dcooperdalrymple/kaypro-usb-keyboard-adapter/hardware/kaypro-usb.kicad_sch

## KiCad design hardware/kaypro-usb.kicad_sch (2023-10-24)

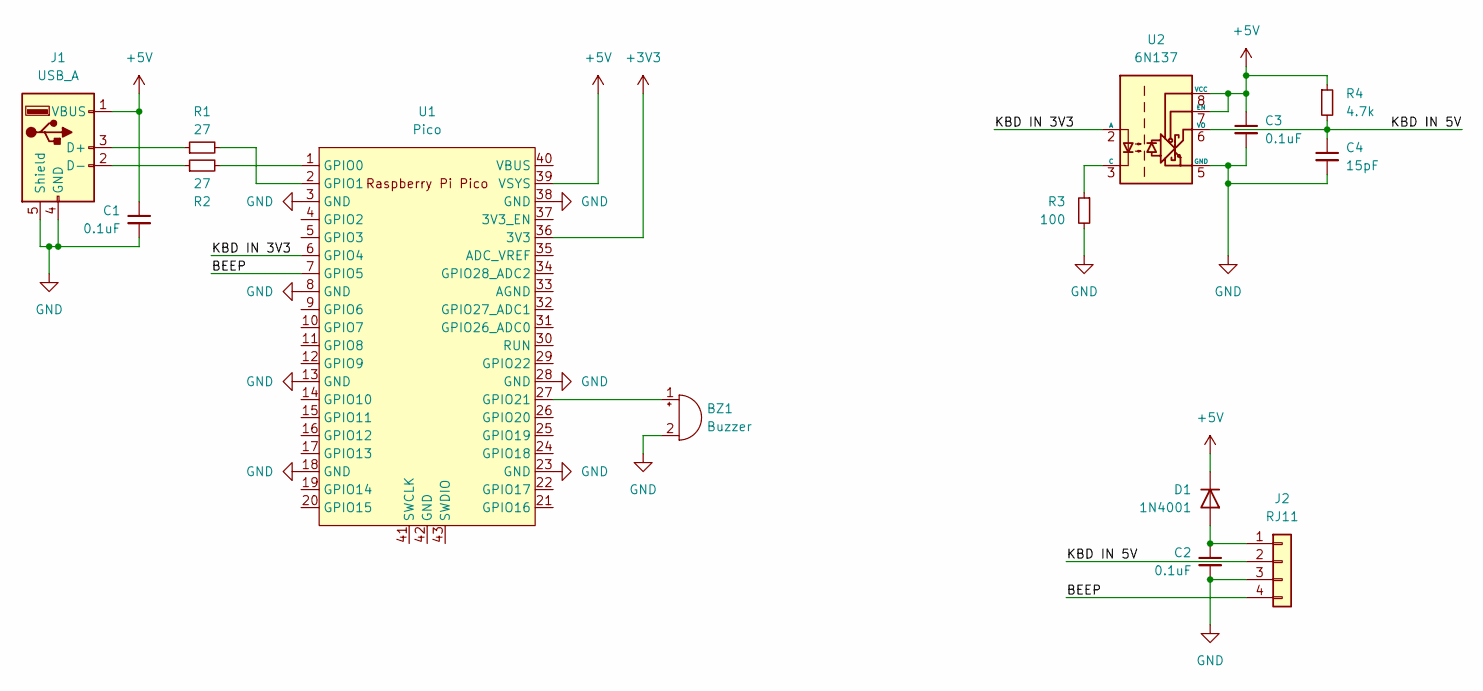
[picture p3: schematic kaypro-usb.kicad_sch]

Parts:
BZ1: Buzzer
C1, C2, C3: 0.1uF
C4: 15pF
D1: 1N4001; D_DO-41_SOD81_P10.16mm_Horizontal
J1: USB_A
J2: RJ11
R1, R2: 27
R3: 100
R4: 4.7k
U1: Pico; RPi_Pico_SMD_TH
U2: 6N137; DIP-8_W7.62mm

Connections:
+3V3: U1.36 (3V3)
+5V: C1.1, C3.1, D1.1 (K), J1.1 (VBUS), R4.1, U1.39 (VSYS), U2.7 (EN), U2.8 (VCC)
BEEP: J2.4, U1.7 (GPIO5)
GND: BZ1.2 (+), C1.2, C2.2, C3.2, C4.2, J1.4 (GND), J1.5 (Shield), J2.3, R3.2, U1.3 (GND), U1.8 (GND), U1.13 (GND), U1.18 (GND), U1.23 (GND), U1.28 (GND), U1.38 (GND), U2.5 (GND)
KBD IN 3V3: U1.6 (GPIO4), U2.2 (A)
KBD IN 5V: C4.1, J2.2, R4.2, U2.6 (VO)
unnamed: BZ1.1 (-), U1.27 (GPIO21)
unnamed: C2.1, D1.2 (A), J2.1
unnamed: J1.2 (D-), R2.1
unnamed: J1.3 (D+), R1.1
unnamed: R1.2, U1.2 (GPIO1)
unnamed: R2.2, U1.1 (GPIO0)
unnamed: R3.1, U2.3 (C)
