dcooperdalrymple/kaypro-usb-keyboard-adapter/src/uart.c

/**
 * kaypro-usb-keyboard-adapter: uart.c
 * @author Cooper Dalrymple
 * @version 1.0
 * @since 1.0
 */

#include "uart.h"

#include <stdlib.h>
#include "pico/stdlib.h"
#include "hardware/gpio.h"
#include "hardware/uart.h"

#include "config.h"

void uart_start(void) {

    // Set UART speed
    uart_init(UART_ID, UART_BAUD_RATE);

    // Set data format
    uart_set_format(UART_ID, UART_DATA_BITS, UART_STOP_BITS, UART_PARITY);

    // Set UART pins
    gpio_set_function(UART_TX_PIN, GPIO_FUNC_UART);
    gpio_set_function(UART_RX_PIN, GPIO_FUNC_UART);
    gpio_set_outover(UART_TX_PIN, GPIO_OVERRIDE_INVERT);

    // Enable Tx and Rx FIFOs on UART
    uart_set_fifo_enabled(UART_ID, true);

    // Disable cr/lf conversion on Tx
    uart_set_translate_crlf(UART_ID, false);

}

void uart_write(uint8_t val) {
    uart_putc_raw(UART_ID, val);
}
